cosmith/tortu/embedded/tortu/src/TortuLogo.h

// array size is 17777
static const byte TortuLogo[] PROGMEM = {
    0x89, 0x50, 0x4e, 0x47, 0x0d, 0x0a, 0x1a, 0x0a, 0x00, 0x00, 0x00, 0x0d, 0x49, 0x48, 0x44, 0x52,
    0x00, 0x00, 0x00, 0xc8, 0x00, 0x00, 0x00, 0x40, 0x08, 0x06, 0x00, 0x00, 0x00, 0x5f, 0xbb, 0x38,
    0x2b, 0x00, 0x00, 0x00, 0x04, 0x67, 0x41, 0x4d, 0x41, 0x00, 0x00, 0xb1, 0x8f, 0x0b, 0xfc, 0x61,
    0x05, 0x00, 0x00, 0x00, 0x20, 0x63, 0x48, 0x52, 0x4d, 0x00, 0x00, 0x7a, 0x26, 0x00, 0x00, 0x80,
    0x84, 0x00, 0x00, 0xfa, 0x00, 0x00, 0x00, 0x80, 0xe8, 0x00, 0x00, 0x75, 0x30, 0x00, 0x00, 0xea,
    0x60, 0x00, 0x00, 0x3a, 0x98, 0x00, 0x00, 0x17, 0x70, 0x9c, 0xba, 0x51, 0x3c, 0x00, 0x00, 0x00,
    0x84, 0x65, 0x58, 0x49, 0x66, 0x4d, 0x4d, 0x00, 0x2a, 0x00, 0x00, 0x00, 0x08, 0x00, 0x05, 0x01,
    0x12, 0x00, 0x03, 0x00, 0x00, 0x00, 0x01, 0x00, 0x01, 0x00, 0x00, 0x01, 0x1a, 0x00, 0x05, 0x00,
    0x00, 0x00, 0x01, 0x00, 0x00, 0x00, 0x4a, 0x01, 0x1b, 0x00, 0x05, 0x00, 0x00, 0x00, 0x01, 0x00,
    0x00, 0x00, 0x52, 0x01, 0x28, 0x00, 0x03, 0x00, 0x00, 0x00, 0x01, 0x00, 0x02, 0x00, 0x00, 0x87,
    0x69, 0x00, 0x04, 0x00, 0x00, 0x00, 0x01, 0x00, 0x00, 0x00, 0x5a, 0x00, 0x00, 0x00, 0x00, 0x00,
    0x00, 0x00, 0x48, 0x00, 0x00, 0x00, 0x01, 0x00, 0x00, 0x00, 0x48, 0x00, 0x00, 0x00, 0x01, 0x00,
    0x03, 0xa0, 0x01, 0x00, 0x03, 0x00, 0x00, 0x00, 0x01, 0x00, 0x01, 0x00, 0x00, 0xa0, 0x02, 0x00,
    0x04, 0x00, 0x00, 0x00, 0x01, 0x00, 0x00, 0x00, 0xc8, 0xa0, 0x03, 0x00, 0x04, 0x00, 0x00, 0x00,
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
    0x61, 0x3e, 0x0a, 0x19, 0x5e, 0xe1, 0x07, 0x00, 0x00, 0x40, 0x00, 0x49, 0x44, 0x41, 0x54, 0x78,
    0x01, 0xed, 0x7d, 0x07, 0x60, 0x15, 0xc5, 0xf6, 0xf7, 0xd9, 0x72, 0x6b, 0x7a, 0xef, 0x09, 0x29,
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
